romain-viollette/SevenSegmentsDisplay/hardware/version_2013_11/photo/SevenSegmentsDisplay_version_2013_11 (8).JPG

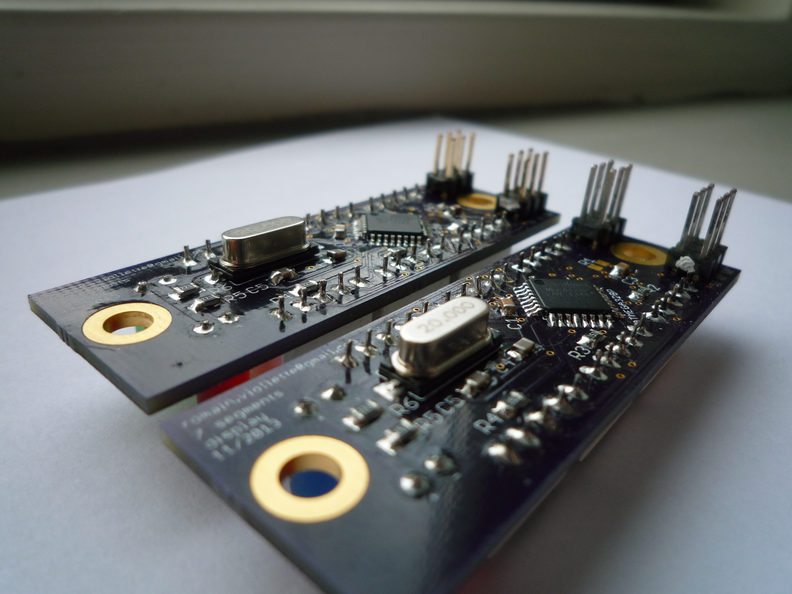
hardware/version_2013_11/photo/SevenSegmentsDisplay_version_2013_11 (8).JPG
